cdudzek/Whack-A-Thingy/Fritzing/Target PCB/SVG/Target%204x%20Rev%201_etch_silk_top.png

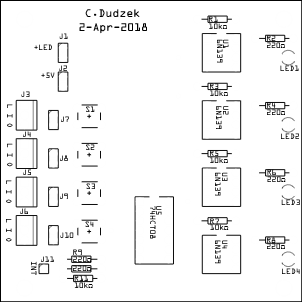
Fritzing/Target PCB/SVG/Target%204x%20Rev%201_etch_silk_top.png
