cdudzek/Whack-A-Thingy/Fritzing/Target PCB/Target 4x Rev 1_bb.png

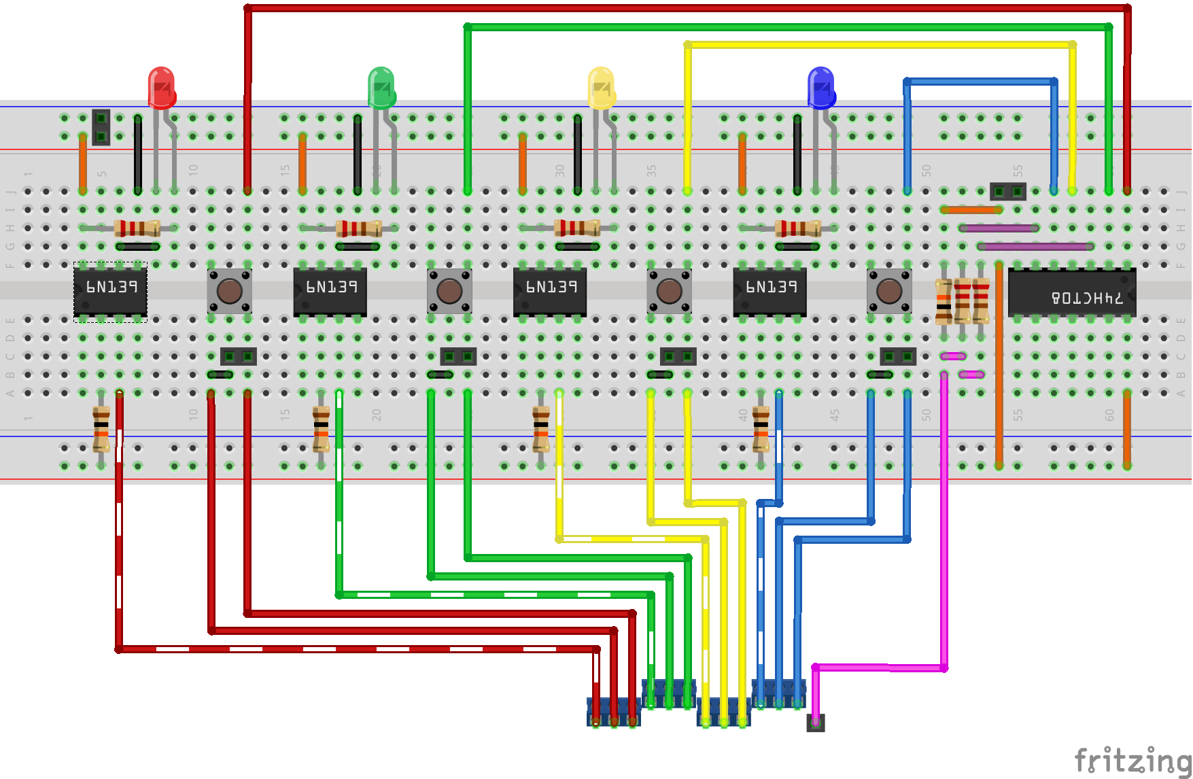
Fritzing/Target PCB/Target 4x Rev 1_bb.png
