cdudzek/Whack-A-Thingy/Photos/Arduino_Mega.jpg

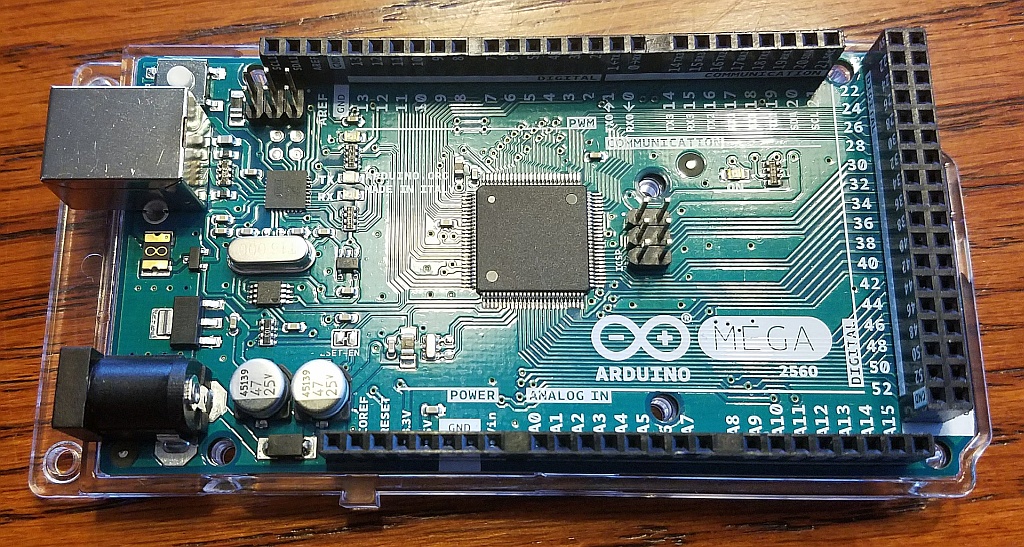
Photos/Arduino_Mega.jpg
