cdudzek/Whack-A-Thingy/Photos/Button_Switch.jpg

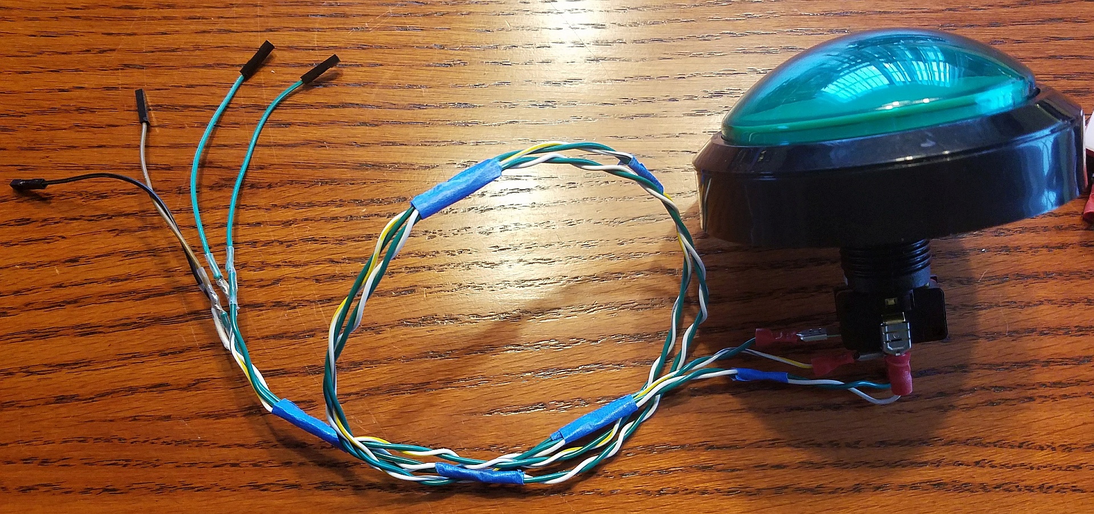
Photos/Button_Switch.jpg
