cdudzek/Whack-A-Thingy/Photos/Buttons.jpg

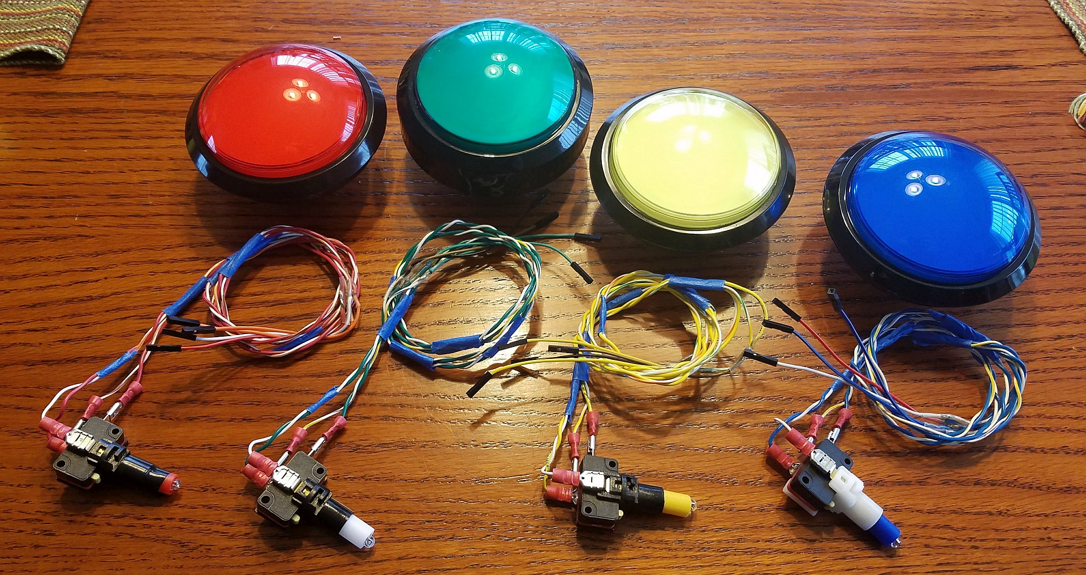
Photos/Buttons.jpg
