cdudzek/Whack-A-Thingy/Photos/PCB.png

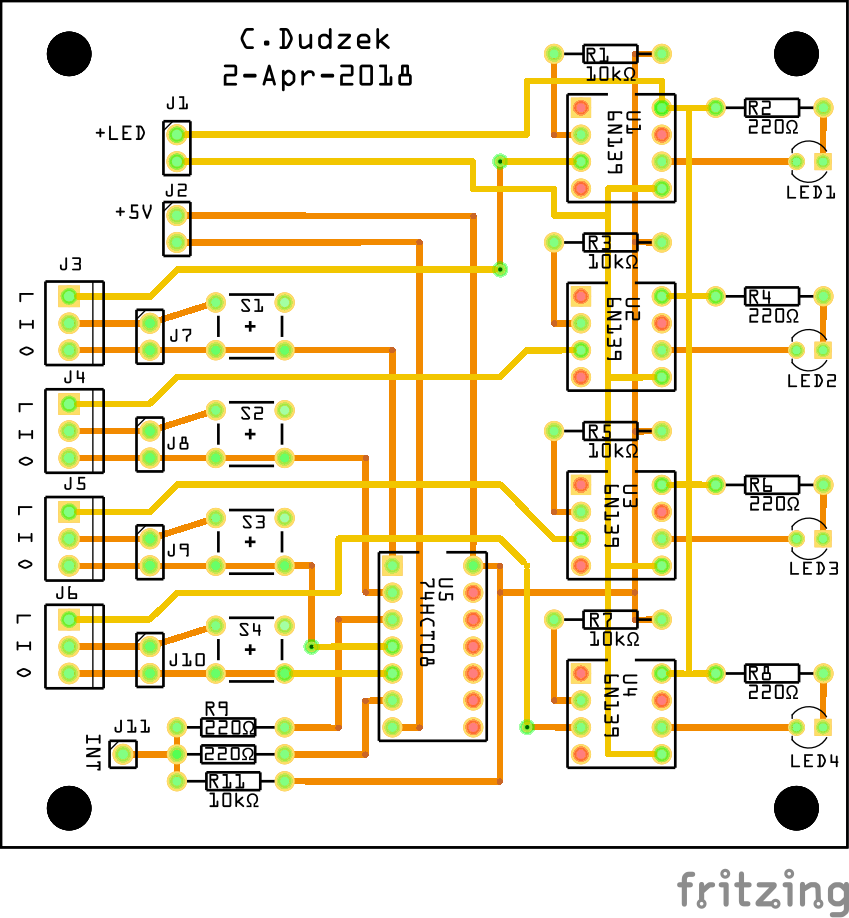
Photos/PCB.png
