cdudzek/Whack-A-Thingy/Photos/PCB_Cables.jpg

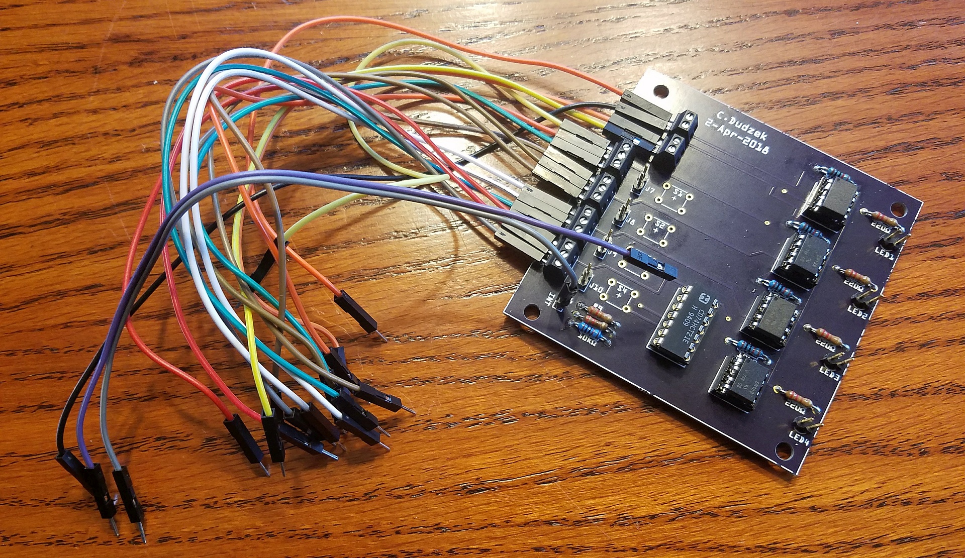
Photos/PCB_Cables.jpg
