cdudzek/Whack-A-Thingy/Photos/PCB_Connectors.png

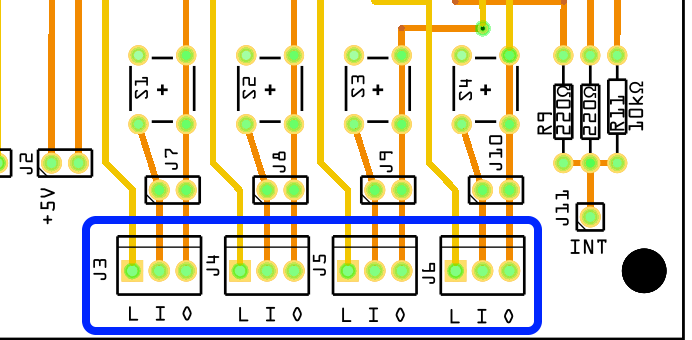
Photos/PCB_Connectors.png
