cdudzek/Whack-A-Thingy/Photos/Power_Switch.jpg

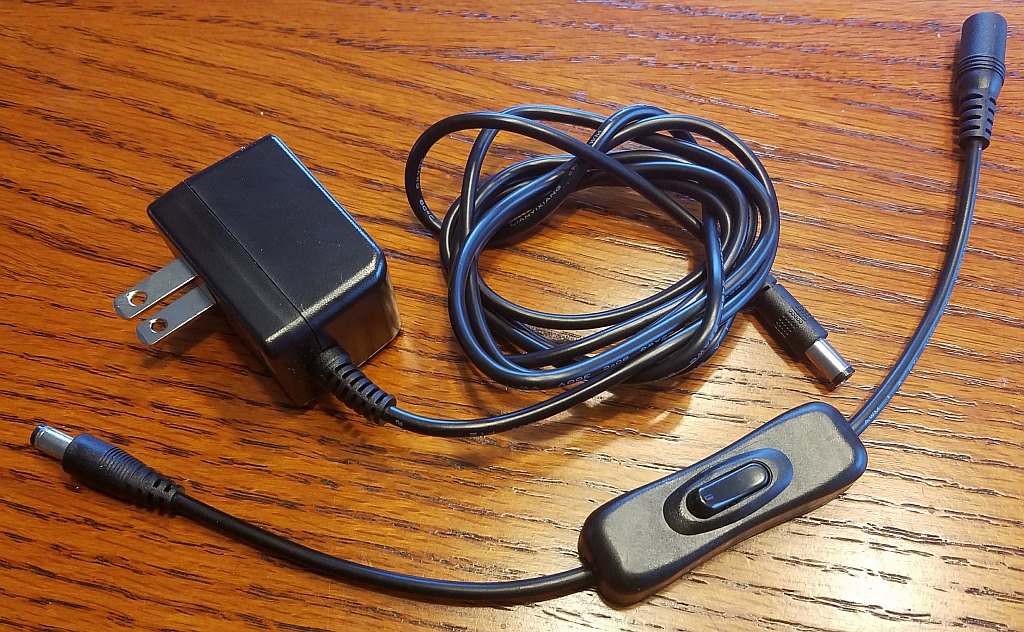
Photos/Power_Switch.jpg
