cdudzek/Whack-A-Thingy/Photos/RGB_LCD.jpg

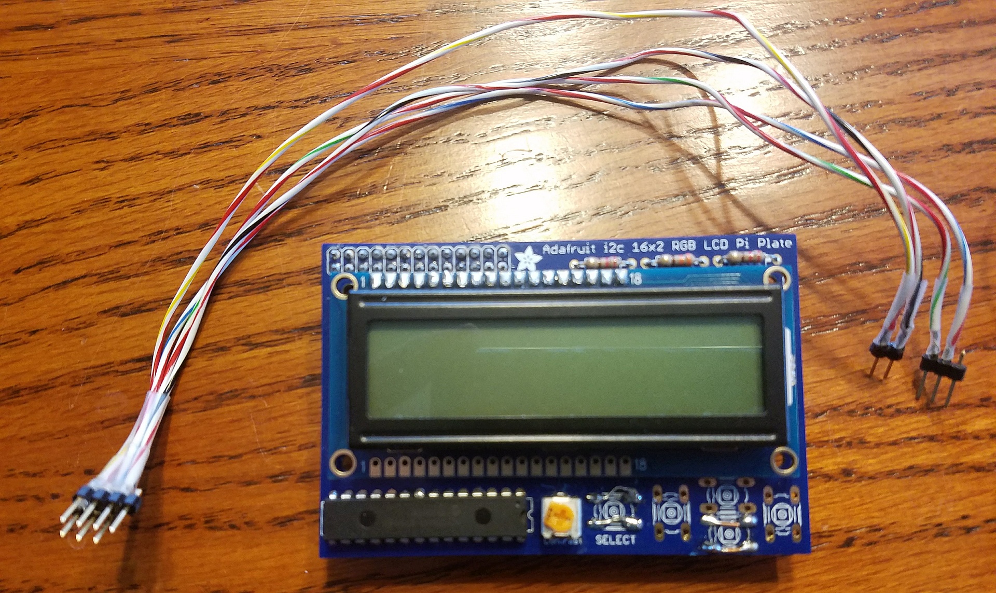
Photos/RGB_LCD.jpg
