cdudzek/Whack-A-Thingy/Photos/Switch_Harness.jpg

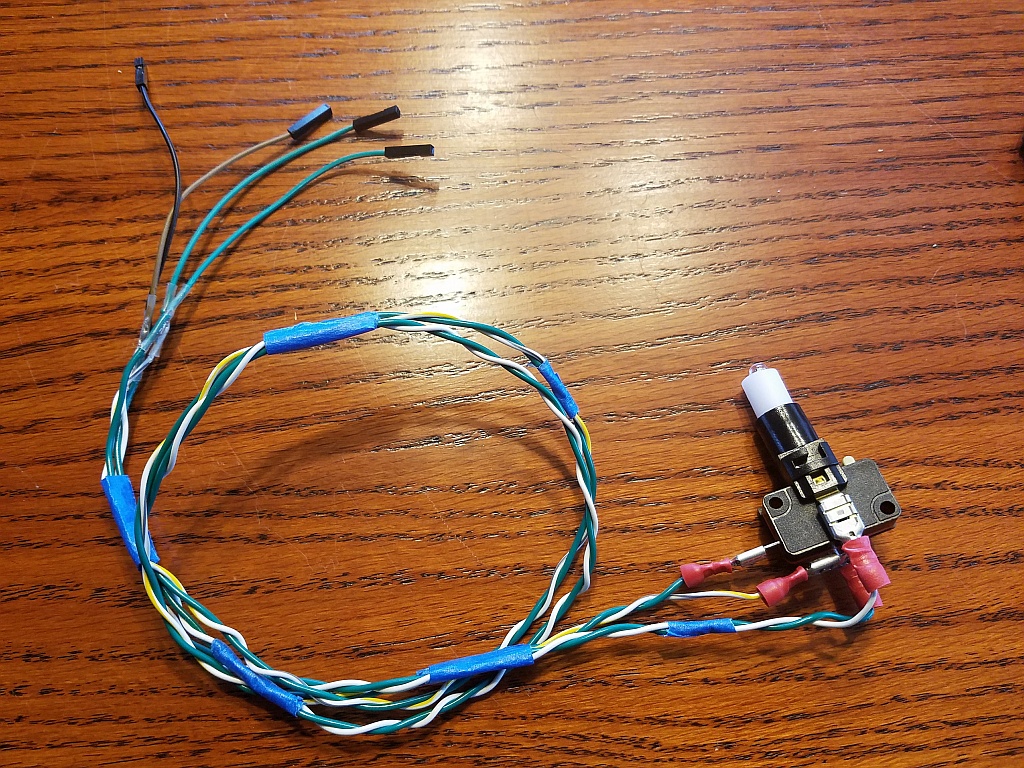
Photos/Switch_Harness.jpg
