cdudzek/Whack-A-Thingy/Photos/User_Buttons.jpg

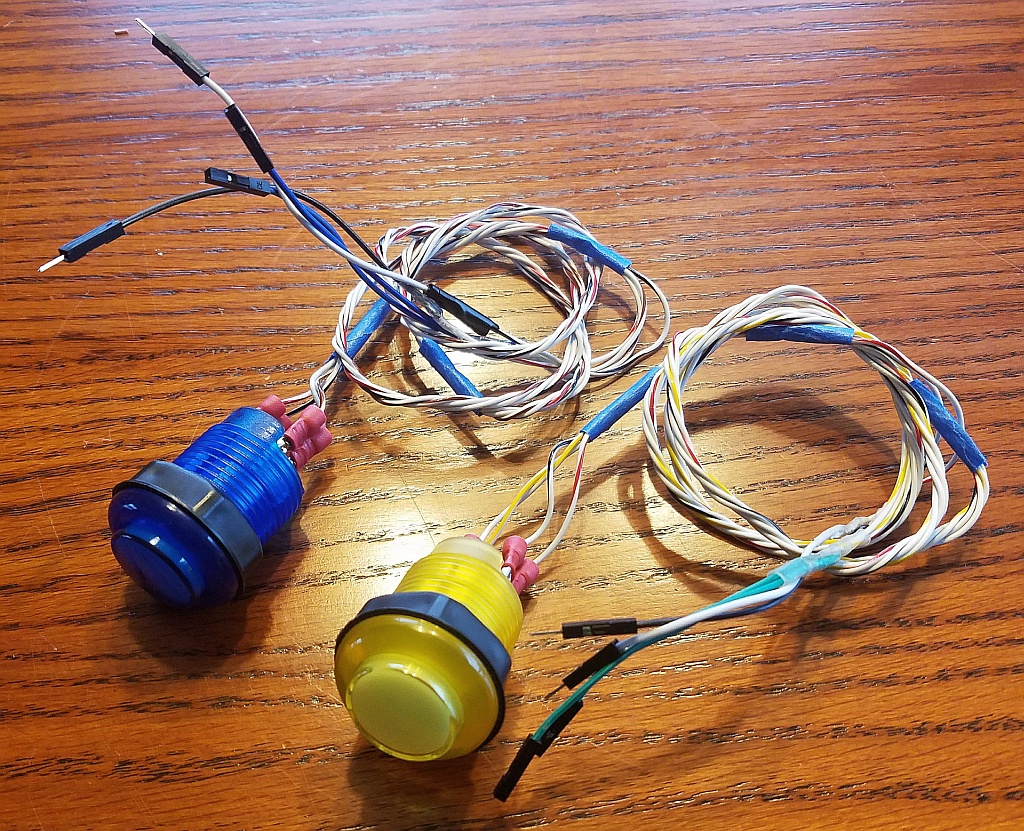
Photos/User_Buttons.jpg
