cdudzek/Whack-A-Thingy/Photos/Wooden_Board.jpg

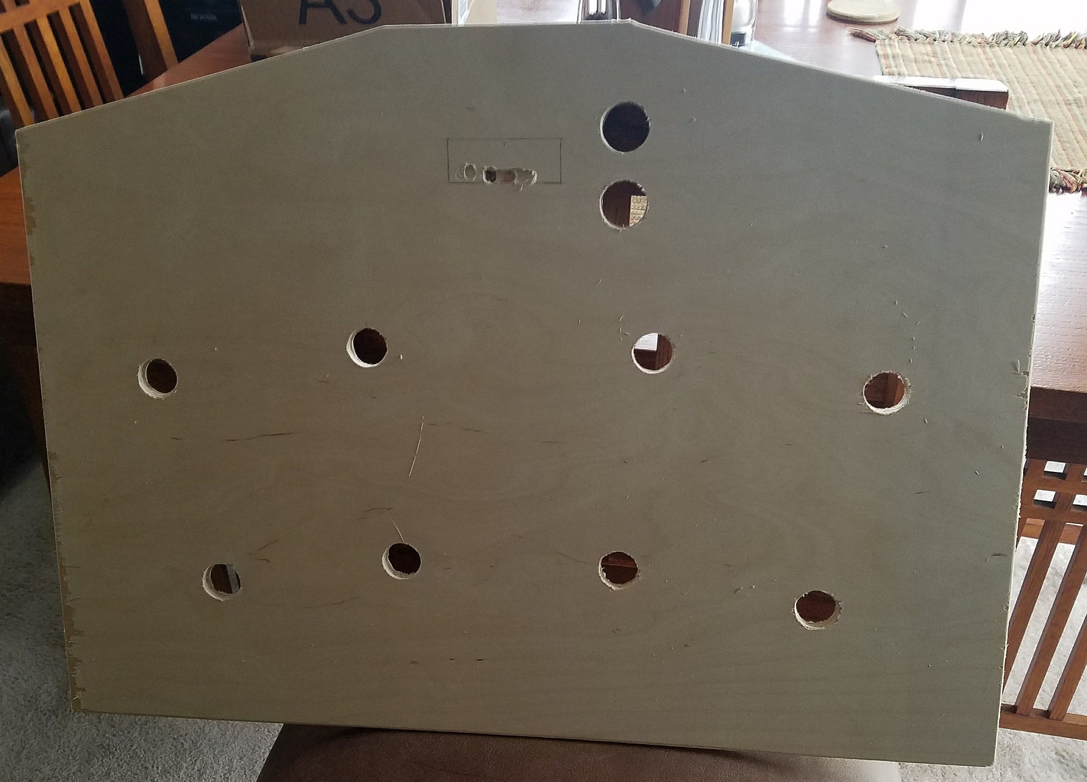
Photos/Wooden_Board.jpg
