cdudzek/Whack-A-Thingy/Photos/All_Test_Parts.jpg

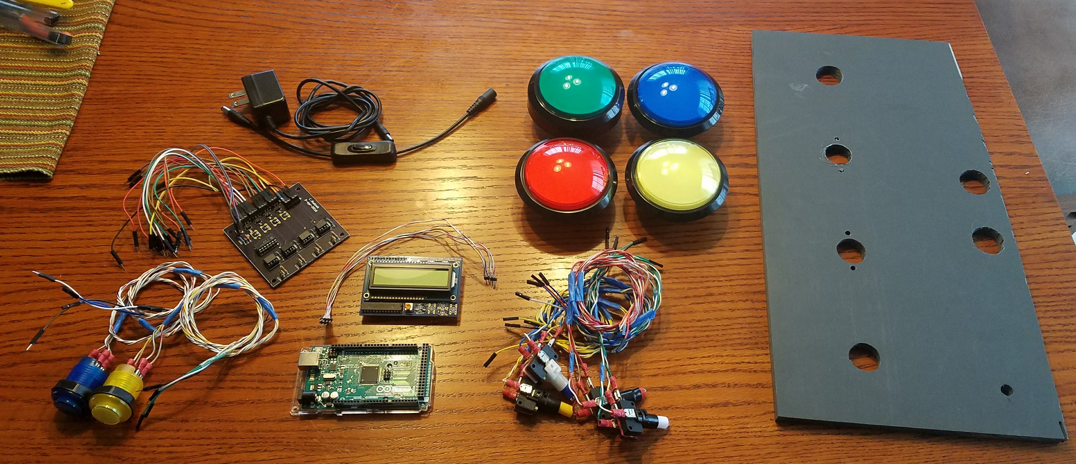
Photos/All_Test_Parts.jpg
