cdudzek/Whack-A-Thingy/Photos/PCB_Parts.jpg

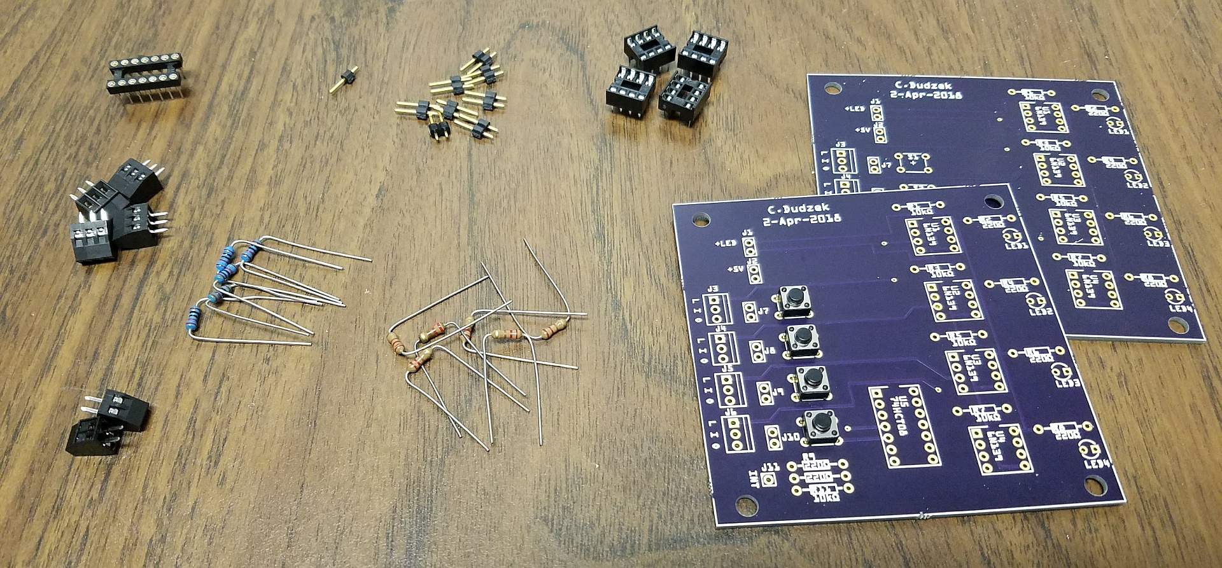
Photos/PCB_Parts.jpg
